vgamaev/ESPMDDEVICE/RF433MHZ.h

#ifndef RF433MHZ_h
#define RF433MHZ_h

#include "ESPMDDEVICE.H"

#ifdef RF433MHZ

#include <Arduino.h>
#include <RCSwitch.h>
#include <ESP8266WebServer.h>
#include <ESP8266HTTPClient.h>
#include "ESPEEPROM.h"

extern HTTPClient http; // веб клиент
extern unsigned long code433;

extern String VersionCode;
extern String Version433MHz ;

void Resiver433();

void Start433();

#endif
#endif
